mneygri56/Operation-Yeet-the-Pi/Pictures/Lightly melted booster.jpg

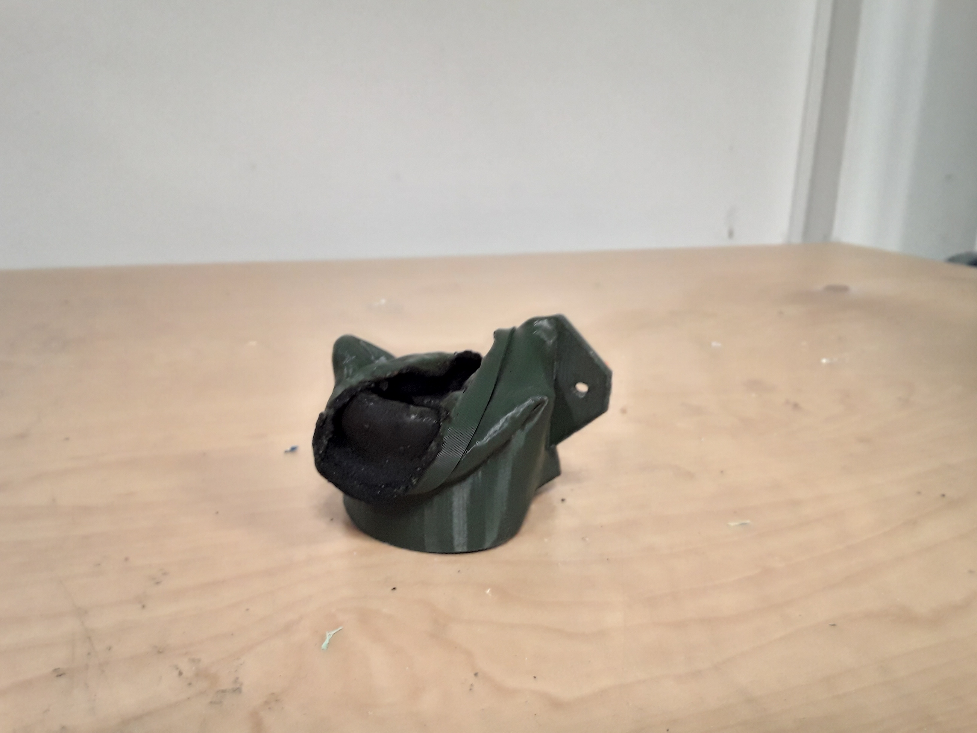
Pictures/Lightly melted booster.jpg
